gaffo/papr/hardware/ammo_case/OuterFilterMountPlate.stl

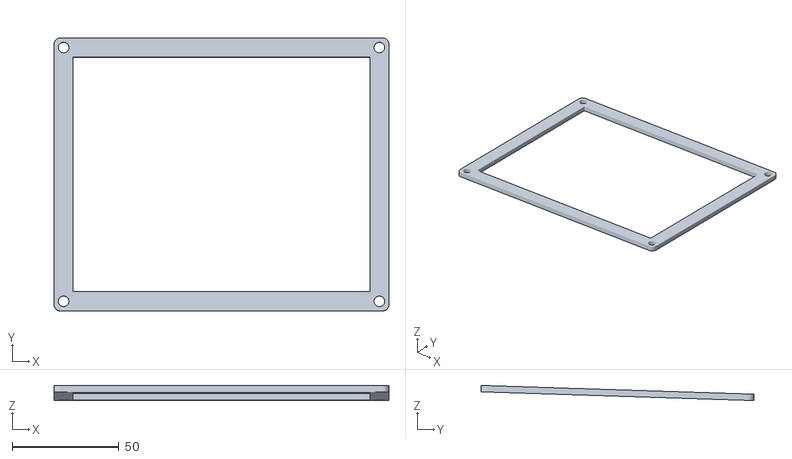
[picture p15: CAD file, 2020-04-26]
hardware/ammo_case/OuterFilterMountPlate.stl
157.0 x 128.0 x 7.10
